jpasqua/FauxMac/images/Actual/Full_Portrait_Kbd_1.jpeg

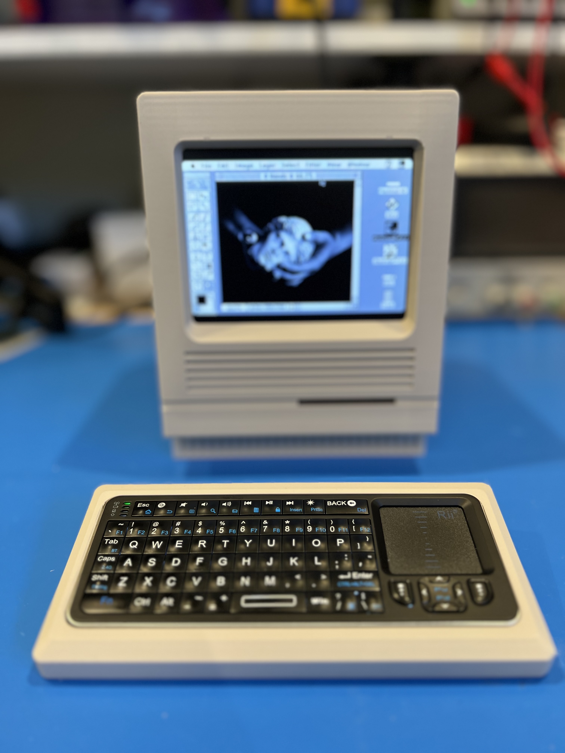
images/Actual/Full_Portrait_Kbd_1.jpeg
