jpasqua/FauxMac/images/Model/Keyboard_Shell_Supports.jpeg

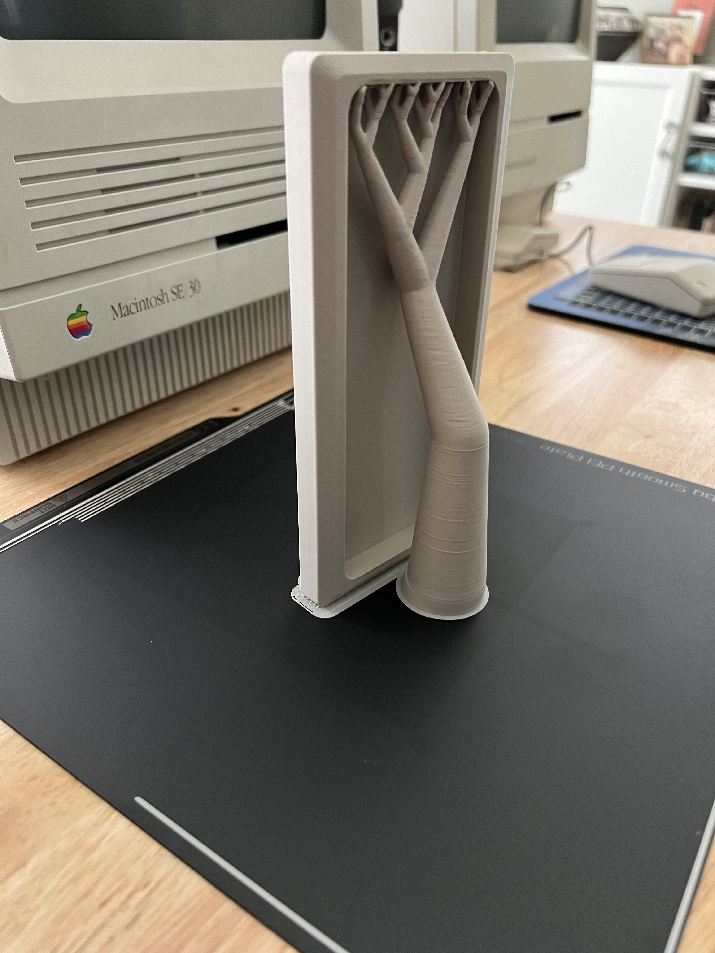
images/Model/Keyboard_Shell_Supports.jpeg
