jpasqua/FauxMac/images/SE30.jpg

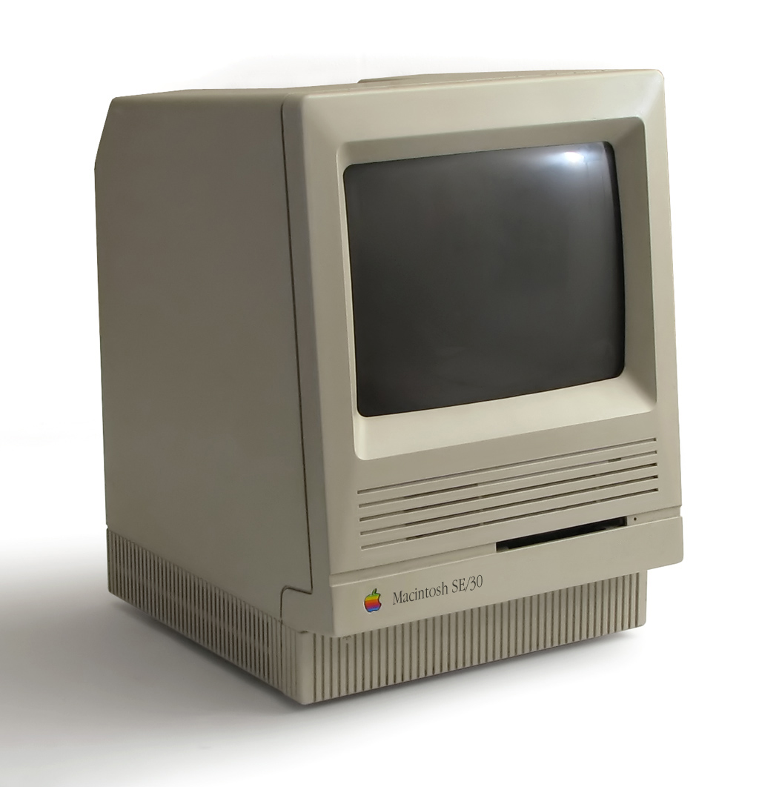
images/SE30.jpg
